vvip-68/GyverMatrixWiFi/Android/images/dot_matrix.png

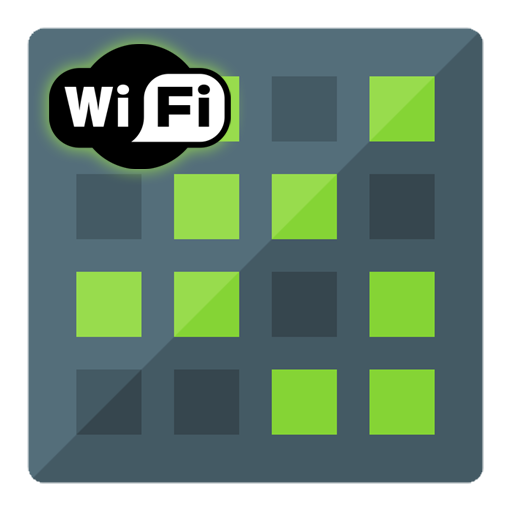
Android/images/dot_matrix.png
