vvip-68/GyverMatrixWiFi/Android/images/Hue_alpha.png

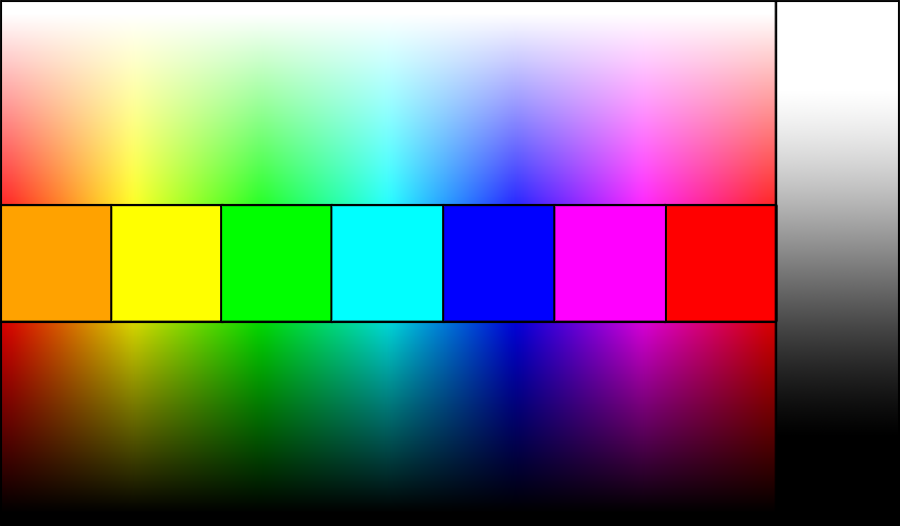
Android/images/Hue_alpha.png
