vvip-68/GyverMatrixWiFi/image decoding/gifs/8-bit_dance_red.gif

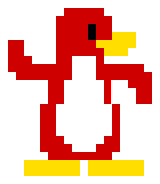
image decoding/gifs/8-bit_dance_red.gif
