vvip-68/GyverMatrixWiFi/image decoding/gifs/8bit_e78edc_811577.gif

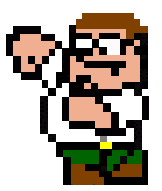
image decoding/gifs/8bit_e78edc_811577.gif
