vvip-68/GyverMatrixWiFi/image decoding/gifs/8x8/Superheroes/Superheroes.png

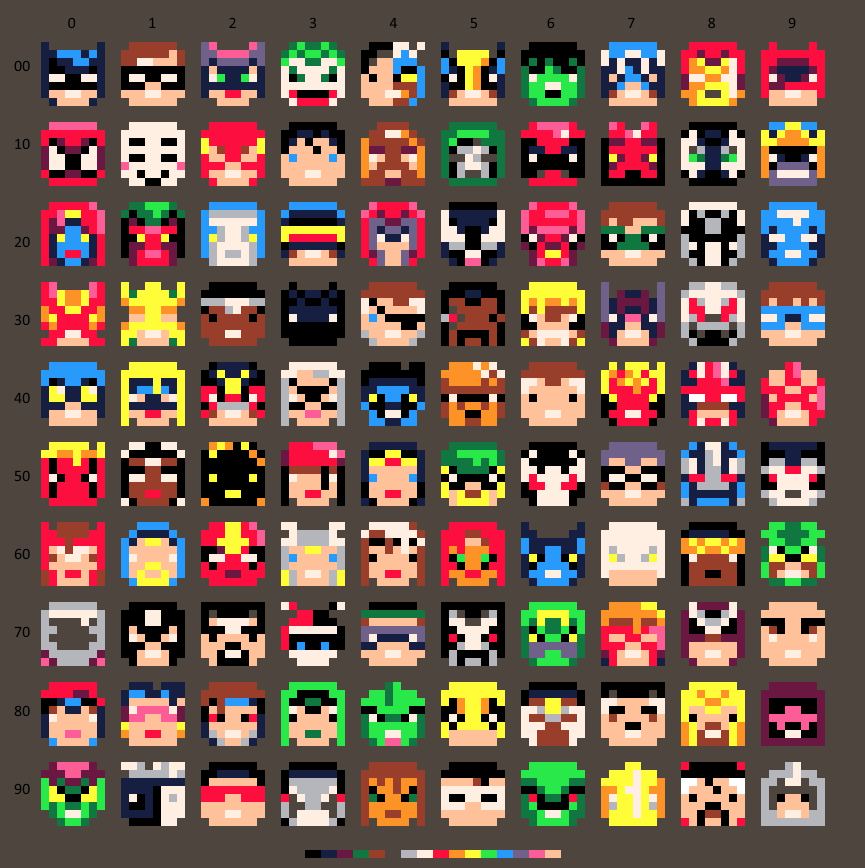
image decoding/gifs/8x8/Superheroes/Superheroes.png
