vvip-68/GyverMatrixWiFi/image decoding/gifs/8x8/VideogameCharacters/VideogameCharacters.png

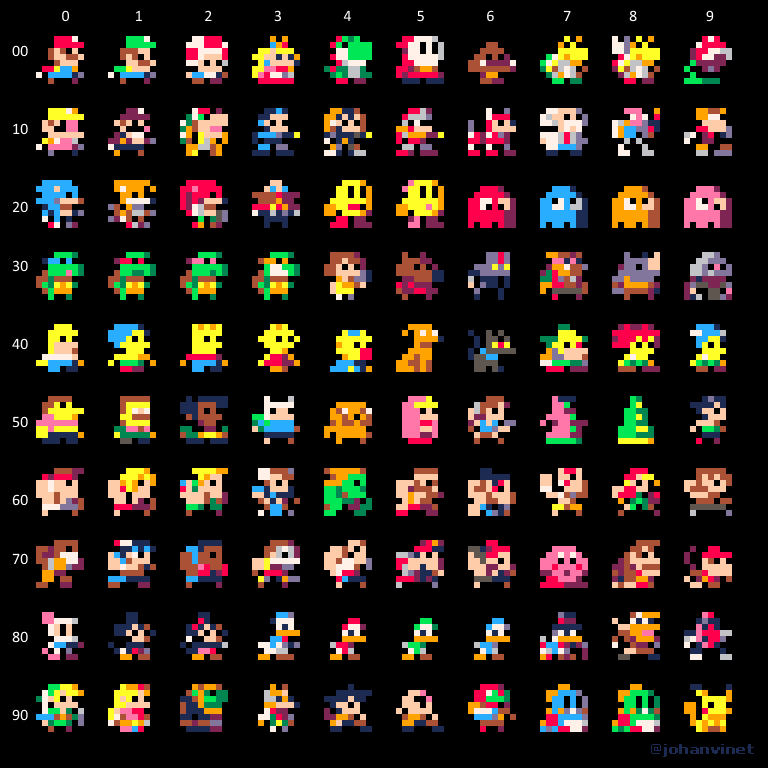
image decoding/gifs/8x8/VideogameCharacters/VideogameCharacters.png
