vvip-68/GyverMatrixWiFi/image decoding/gifs/60066832178daa8c864df8cbb47f908b34b75229.gif

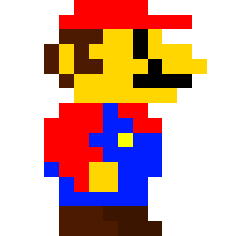
image decoding/gifs/60066832178daa8c864df8cbb47f908b34b75229.gif
