vvip-68/GyverMatrixWiFi/image decoding/gifs/asd.jpg

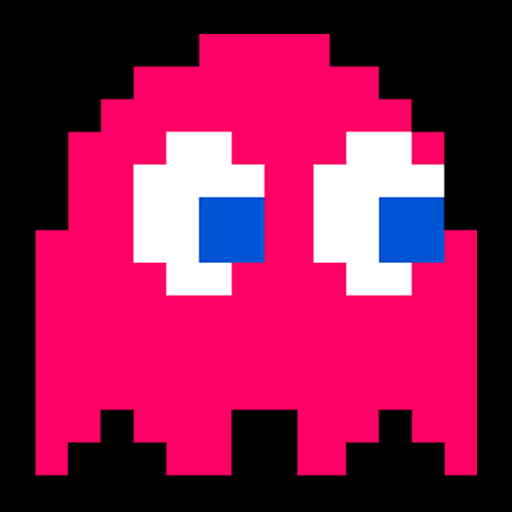
image decoding/gifs/asd.jpg
