vvip-68/GyverMatrixWiFi/image decoding/gifs/bac494cc944dbecb-me-8bit-terraria-style-gif-by-avthecreeper-on-deviantart.gif

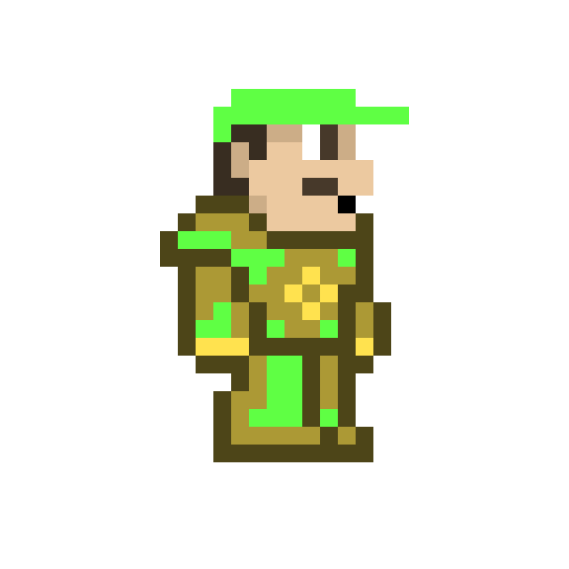
image decoding/gifs/bac494cc944dbecb-me-8bit-terraria-style-gif-by-avthecreeper-on-deviantart.gif
