vvip-68/GyverMatrixWiFi/image decoding/gifs/d8q91xd-37d3a5f7-6120-4784-a24a-eec837a43671.gif

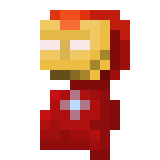
image decoding/gifs/d8q91xd-37d3a5f7-6120-4784-a24a-eec837a43671.gif
