vvip-68/GyverMatrixWiFi/image decoding/gifs/db7e7il-261c622e-b4ed-433d-9d11-8a8a13b2ce55.gif

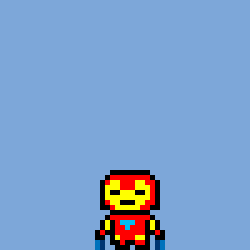
image decoding/gifs/db7e7il-261c622e-b4ed-433d-9d11-8a8a13b2ce55.gif
