vvip-68/GyverMatrixWiFi/image decoding/gifs/fire.gif

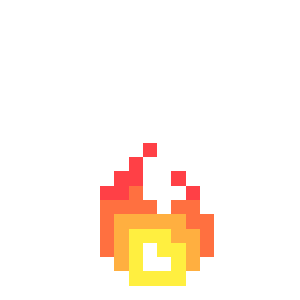
image decoding/gifs/fire.gif
