vvip-68/GyverMatrixWiFi/image decoding/gifs/fry-sprite-5fps.gif

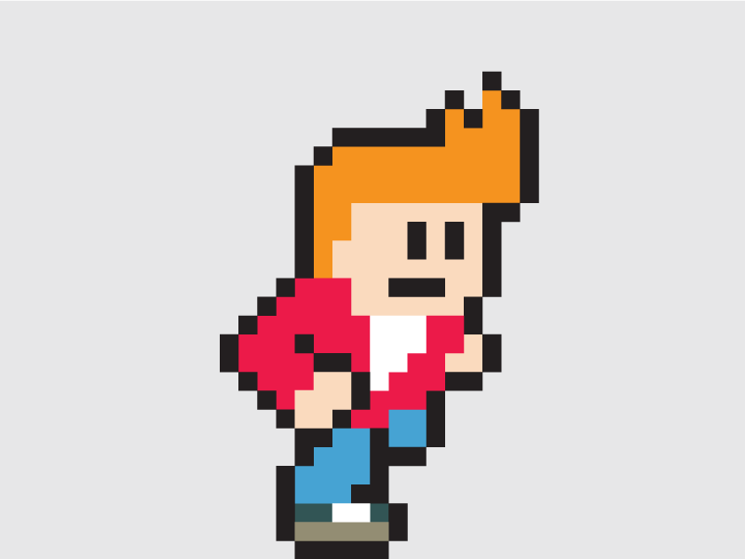
image decoding/gifs/fry-sprite-5fps.gif
