vvip-68/GyverMatrixWiFi/image decoding/gifs/megaman-running-gif-8.gif

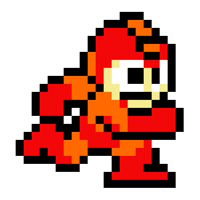
image decoding/gifs/megaman-running-gif-8.gif
