vvip-68/GyverMatrixWiFi/image decoding/gifs/source.gif

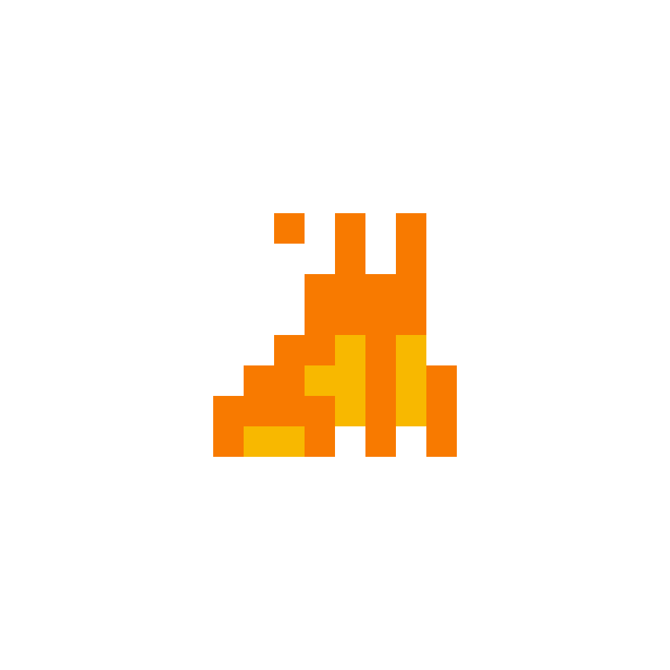
image decoding/gifs/source.gif
