vvip-68/GyverMatrixWiFi/image decoding/gifs/tenor (1).gif

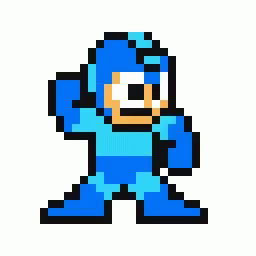
image decoding/gifs/tenor (1).gif
