vvip-68/GyverMatrixWiFi/image decoding/gifs/tenor (2).gif

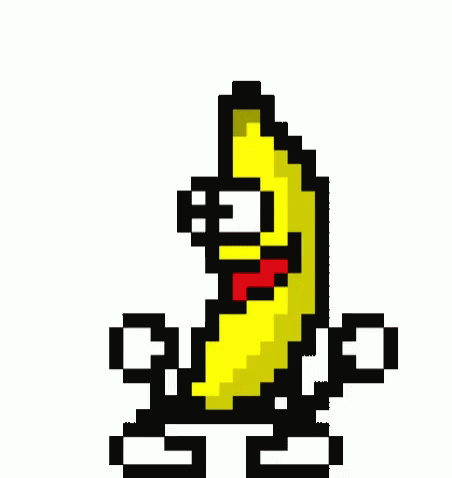
image decoding/gifs/tenor (2).gif
