vvip-68/GyverMatrixWiFi/image decoding/gifs/tenor.gif

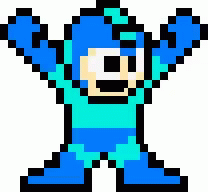
image decoding/gifs/tenor.gif
