vvip-68/GyverMatrixWiFi/image decoding/gifs/transparent-flames-8-bit-6.gif

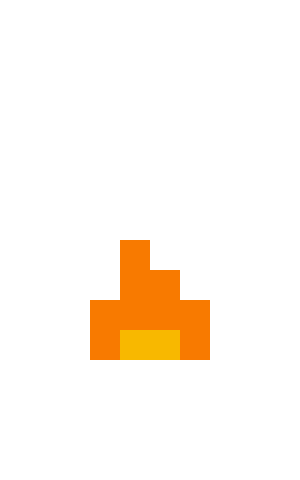
image decoding/gifs/transparent-flames-8-bit-6.gif
