vvip-68/GyverMatrixWiFi/image decoding/gifs/джэ.jpg

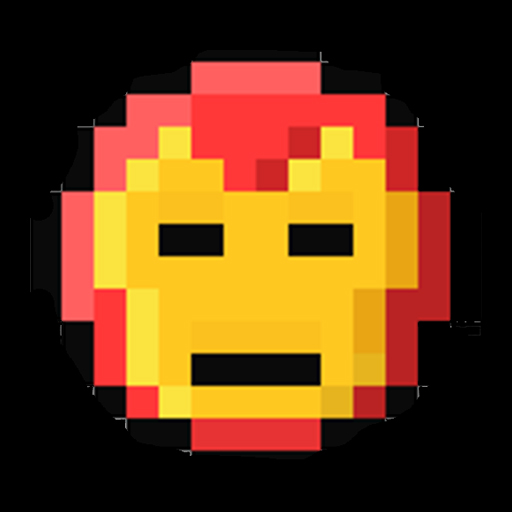
image decoding/gifs/джэ.jpg
