vvip-68/GyverMatrixWiFi/schemes/grid.png

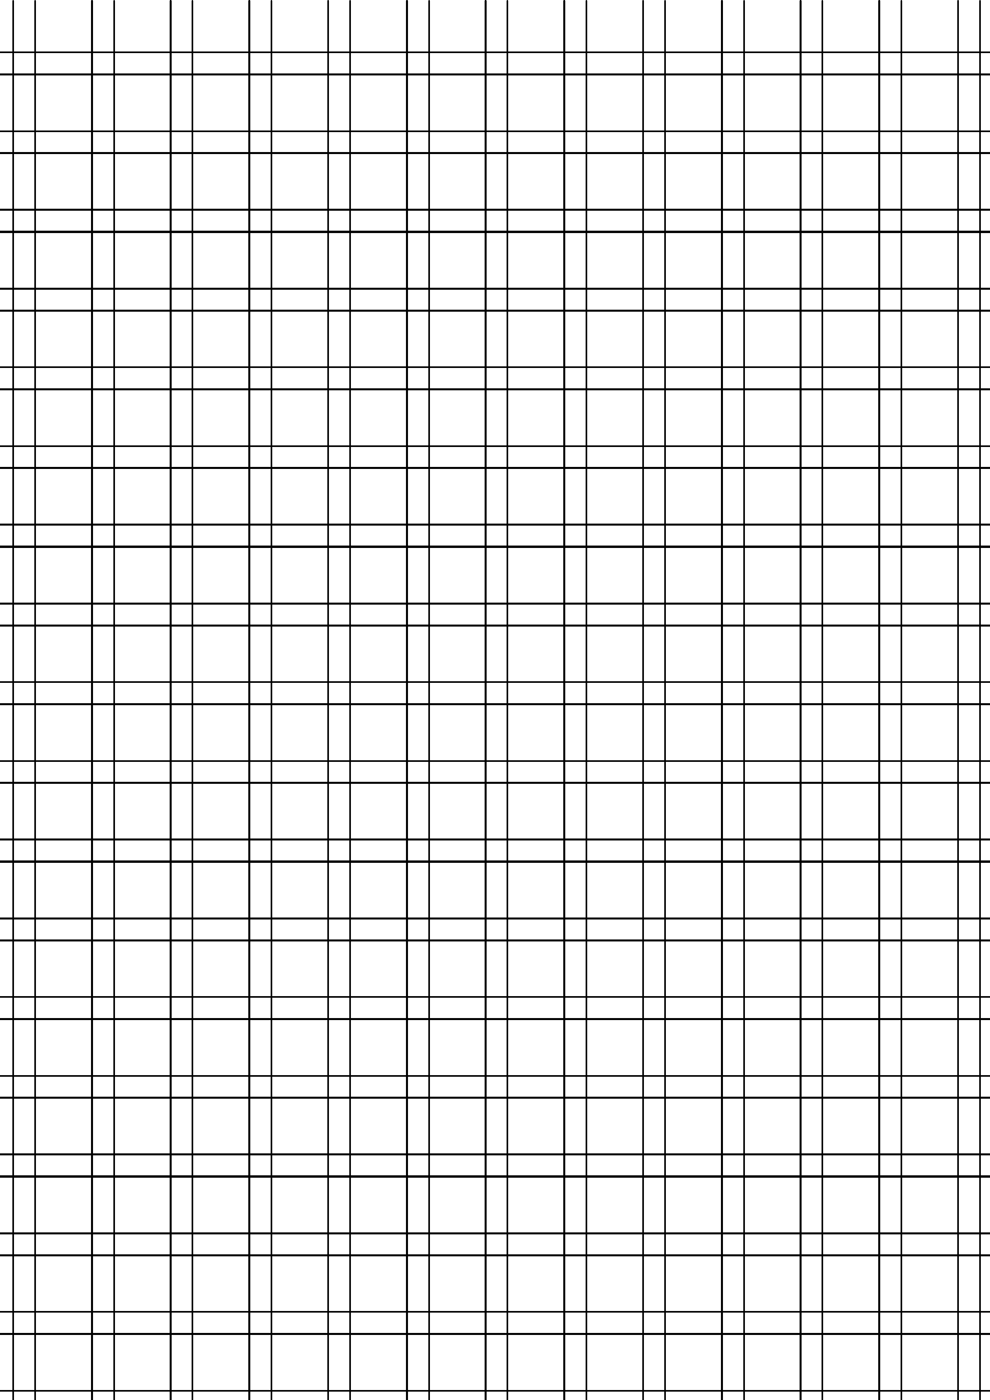
schemes/grid.png
