vvip-68/GyverMatrixWiFi/schemes/scheme4.jpg

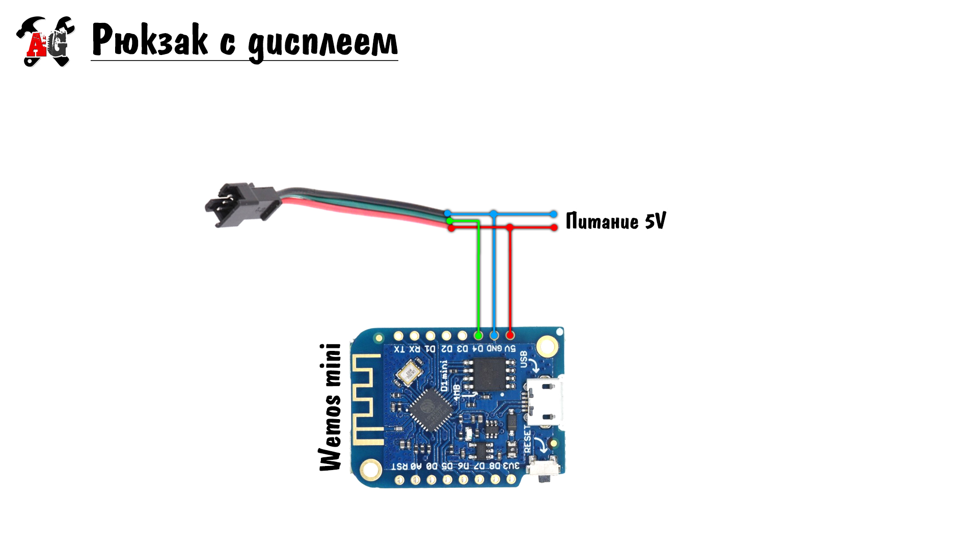
schemes/scheme4.jpg
