vvip-68/GyverMatrixWiFi/schemes/scheme5.jpg

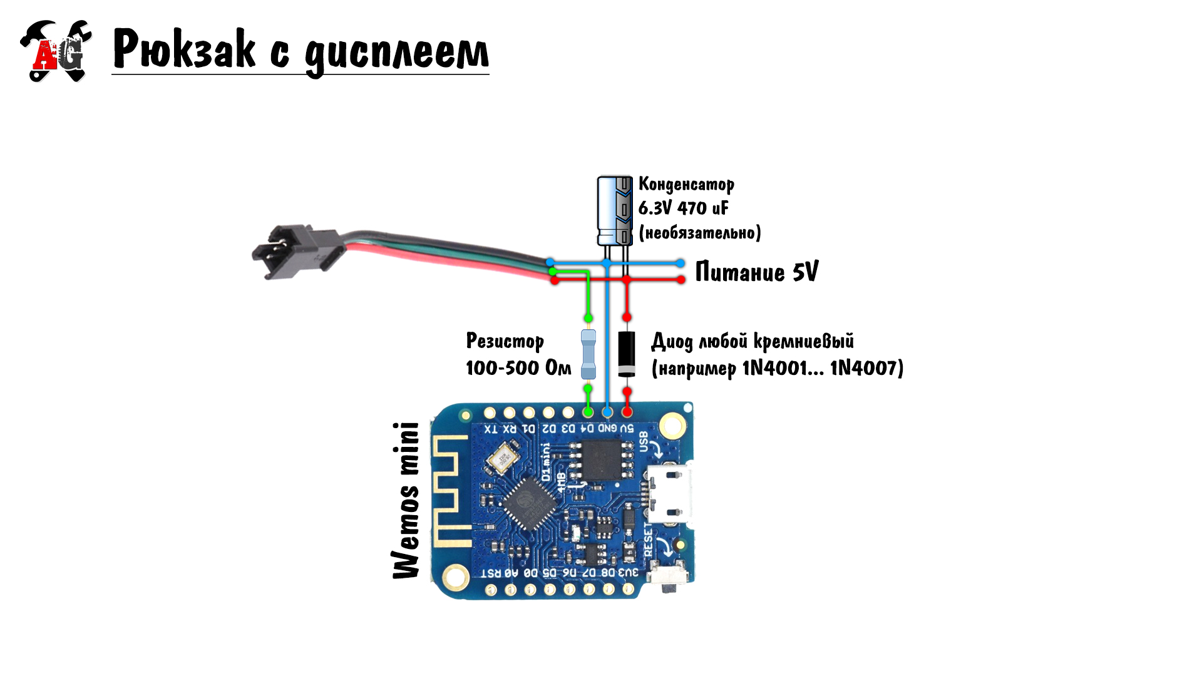
schemes/scheme5.jpg
