vvip-68/GyverMatrixWiFi/firmware/GyverMatrixOS_v1.15/custom.ino

// свой список режимов

// ************************ НАСТРОЙКИ ************************
#define SHOW_FULL_TEXT 1    // не переключать режим, пока текст не покажется весь
#define SHOW_TEXT_ONCE 1    // показывать бегущий текст только 1 раз

/*
   Режимы:
    clockRoutine();       // часы на чёрном фоне

   Эффекты:
    sparklesRoutine();    // случайные цветные гаснущие вспышки
    snowRoutine();        // снег
    matrixRoutine();      // "матрица"
    starfallRoutine();    // звездопад (кометы)
    ballRoutine();        // квадратик
    ballsRoutine();       // шарики
    rainbowRoutine();     // радуга во всю матрицу горизонтальная
    rainbowDiagonalRoutine();   // радуга во всю матрицу диагональная
    fireRoutine();        // огонь
    lightBallsRoutine()   // пейнтбол
    lightersRoutine()     // светляки

  Крутые эффекты "шума":
    madnessNoise();       // цветной шум во всю матрицу
    cloudNoise();         // облака
    lavaNoise();          // лава
    plasmaNoise();        // плазма
    rainbowNoise();       // радужные переливы
    rainbowStripeNoise(); // полосатые радужные переливы
    zebraNoise();         // зебра
    forestNoise();        // шумящий лес
    oceanNoise();         // морская вода

  Игры:
    snakeRoutine();     // змейка
    tetrisRoutine();    // тетрис
    mazeRoutine();      // лабиринт
    runnerRoutine();    // бегалка прыгалка
    arkanoidRoutine();  // арканоид

  Бегущая строка:
    fillString("Ваш текст", цвет);    // цвет вида 0x00ff25 или CRGB::Red и проч. цвета
    fillString("Ваш текст", 1);       // радужный перелив текста
    fillString("Ваш текст", 2);       // каждая буква случайным цветом!

  Рисунки и анимации:
    loadImage(<название массива>);    // основная функция вывода картинки
    imageRoutine();                   // пример использования
    animation(<n>);                   // пример анимации
*/

byte lastOverlayMode;
void customRoutine() {

  if (!gamemodeFlag || isAlarming) {

    // Беугщая строка - таймер внутри fillString (runningText.ino)
    if (!isAlarming && (thisMode == DEMO_TEXT_0 || thisMode == DEMO_TEXT_1 || thisMode == DEMO_TEXT_2)) {
      customModes(thisMode);
    } 

    // Эффекты - возможно наложение часов
    else {
      doEffectWithOverlay(thisMode); 
    }
  } 

  // Игры - таймер внутри игр
  else {
    if (!gamePaused || loadingFlag) customModes(thisMode);
  }
}

void doEffectWithOverlay(byte aMode) {

  if (effectTimer.isReady()) {

#if (OVERLAY_CLOCK == 1)
    bool loadFlag2;
    bool needOverlay = modeCode != MC_TEXT && overlayAllowed();

    if (needOverlay && lastOverlayMode == thisMode) {
      if (!loadingFlag && needUnwrap()) {
        if (showDateInClock && showDateState) {
            calendarOverlayUnwrap(CALENDAR_X, CALENDAR_Y);
        } else {
          if (CLOCK_ORIENT == 0)
            clockOverlayUnwrapH(CLOCK_X, CLOCK_Y);
          else
            clockOverlayUnwrapV(CLOCK_X, CLOCK_Y);
        }
      }
      if (loadingFlag) loadFlag2 = true;
    }
#endif

    customModes(aMode);                // режимы крутятся, пиксели мутятся

    if (millis() - showDateStateLastChange > (showDateState ? showDateDuration : showDateInterval) * 1000L) {
      showDateStateLastChange = millis();
      showDateState = !showDateState;
    }
        
#if (OVERLAY_CLOCK == 1)
    if (needOverlay) {
      if (showDateInClock && showDateState) {
        calendarOverlayWrap(CALENDAR_X, CALENDAR_Y);
      } else {
        if (CLOCK_ORIENT == 0)
          clockOverlayWrapH(CLOCK_X, CLOCK_Y);
        else  
          clockOverlayWrapV(CLOCK_X, CLOCK_Y);
      }
      lastOverlayMode = thisMode;
      if (loadFlag2) {
        setOverlayColors();
        loadFlag2 = false;
      }          
    }
    loadingFlag = false;
#endif
    FastLED.show();
  }
}

void customModes(byte aMode) {  

  switch (aMode) {    
    case DEMO_TEXT_0:              fillString(TEXT_1, CRGB::RoyalBlue); break;
    case DEMO_TEXT_1:              fillString(TEXT_2, 1); break;
    case DEMO_TEXT_2:              fillString(TEXT_3, 2); break;
    case DEMO_NOISE_MADNESS:       madnessNoise(); break;
    case DEMO_NOISE_CLOUD:         cloudNoise(); break;
    case DEMO_NOISE_LAVA:          lavaNoise(); break;
    case DEMO_NOISE_PLASMA:        plasmaNoise(); break;
    case DEMO_NOISE_RAINBOW:       rainbowNoise(); break;
    case DEMO_NOISE_RAINBOW_STRIP: rainbowStripeNoise(); break;
    case DEMO_NOISE_ZEBRA:         zebraNoise(); break;
    case DEMO_NOISE_FOREST:        forestNoise(); break;
    case DEMO_NOISE_OCEAN:         oceanNoise(); break;
    case DEMO_SNOW:                snowRoutine(); break;
    case DEMO_SPARKLES:            sparklesRoutine(); break;
    case DEMO_MATRIX:              matrixRoutine(); break;
    case DEMO_STARFALL:            starfallRoutine(); break;
    case DEMO_BALL:                ballRoutine(); break;
    case DEMO_BALLS:               ballsRoutine(); break;
    case DEMO_RAINBOW:             rainbowRoutine(); break;
    case DEMO_RAINBOW_DIAG:        rainbowDiagonalRoutine(); break;
    case DEMO_FIRE:                fireRoutine(); break;
    case DEMO_SNAKE:               snakeRoutine(); break;
    case DEMO_TETRIS:              tetrisRoutine(); break;
    case DEMO_MAZE:                mazeRoutine(); break;
    case DEMO_RUNNER:              runnerRoutine(); break;
    case DEMO_ARKANOID:            arkanoidRoutine(); break;
    case DEMO_CLOCK:               clockRoutine(); break;
    case DEMO_DAWN_ALARM:          dawnProcedure(); break;
    case DEMO_FILL_COLOR:          fillColorProcedure(); break;
    case DEMO_LIGHTERS:            lightersRoutine(); break;
    case DEMO_PAINTBALL:           lightBallsRoutine(); break;
    case DEMO_SWIRL:               swirlRoutine(); break;

    case DEMO_ANIMATION_1:         animation(1); break;
    /*
    case DEMO_ANIMATION_2:         animation(2); break;
    case DEMO_ANIMATION_3:         animation(3); break;
    case DEMO_ANIMATION_4:         animation(4); break;
    case DEMO_ANIMATION_5:         animation(5); break;
    */
    
    // Специальные режимы - доступные только для вызова из эффекта рассвета - dawnProcedure()
    case DEMO_DAWN_ALARM_SPIRAL:   dawnLampSpiral(); break;
    case DEMO_DAWN_ALARM_SQUARE:   dawnLampSquare(); break;
  }
}

// ********************* ОСНОВНОЙ ЦИКЛ РЕЖИМОВ *******************

static void nextMode() {  
#if (SMOOTH_CHANGE == 1)
  fadeMode = 0;
  modeDir = true;
#else
  nextModeHandler();
#endif
}

static void prevMode() {
#if (SMOOTH_CHANGE == 1)
  fadeMode = 0;
  modeDir = false;
#else
  prevModeHandler();
#endif
}

void nextModeHandler() {

  if (useRandomSequence) {
    setRandomMode2();
    return;
  }
  
  byte aCnt = 0;
  byte curMode = thisMode;

  loadingFlag = true;
  autoplayTimer = millis();  
  
  while (aCnt < MODES_AMOUNT) {
    // Берем следующий режим по циклу режимов
    aCnt++; thisMode++;  
    if (thisMode >= MODES_AMOUNT) thisMode = 0;

    // Если новый режим отмечен флагом "использовать" - используем его, иначе берем следующий (и проверяем его)
    if (getUsageForMode(thisMode)) break;
    
    // Если перебрали все и ни у одного нет флага "использовать" - не обращаем внимание на флаг, используем следующий
    if (aCnt >= MODES_AMOUNT) {
      thisMode = curMode++;
      if (thisMode >= MODES_AMOUNT) thisMode = 0;
      break;
    }  
    #if defined(ESP8266)
    ESP.wdtFeed();  
    #endif
  }

  setModeByModeId(thisMode); 
  autoplayTimer = millis();

  FastLED.clear();
  FastLED.show();
  FastLED.setBrightness(globalBrightness);
}

void prevModeHandler() {

  if (useRandomSequence) {
    setRandomMode2();
    return;
  }

  byte aCnt = 0;
  byte curMode = thisMode;

  while (aCnt < MODES_AMOUNT) {
    // Берем предыдущий режим по циклу режимов
    aCnt++; thisMode--; // thisMode: byte => при переполнении вернет 255 
    if (thisMode >= MODES_AMOUNT) thisMode = MODES_AMOUNT - 1;

    // Если новый режим отмечен флагом "использовать" - используем его, иначе берем следующий (и проверяем его)
    if (getUsageForMode(thisMode)) break;
    
    // Если перебрали все и ни у адного нет флага "использовать" - не обращаем внимание на флаг, используем следующий
    if (aCnt >= MODES_AMOUNT) {
      thisMode = curMode--; // thisMode: byte => при переполнении вернет 255
      if (thisMode >= MODES_AMOUNT) thisMode = MODES_AMOUNT - 1;
      break;
    }   
    
    #if defined(ESP8266)    
    ESP.wdtFeed(); 
    #endif
  }
  
  setModeByModeId(thisMode); 
  autoplayTimer = millis();
  
  FastLED.clear();
  FastLED.show();
  FastLED.setBrightness(globalBrightness);
}

void setTimersForMode(byte aMode) {
  if (runningFlag || aMode == DEMO_TEXT_0 || aMode == DEMO_TEXT_1 || aMode == DEMO_TEXT_2) {
    // Это бегущий текст  
    scrollSpeed = getScrollSpeed();
    if (scrollSpeed == 0) scrollSpeed = 1;
    scrollTimer.setInterval(scrollSpeed);
  } 
  else if (aMode == DEMO_PAINTBALL) {
    // Это эффект Пейнтбол
    effectSpeed = getEffectSpeed(EFFECT_PAINTBALL);  // В этом эффекте параметр "скорость" влияет на количество шариков 1..4 
    effectTimer.setInterval(10);                     // Эффект работает только на высокой скорости
  } 
  /*
  else if (aMode == DEMO_SWIRL) {
    // Это эффект Swirl
    effectSpeed = getEffectSpeed(EFFECT_SWIRL);      // 
    effectTimer.setInterval(10);                     // Этот эффект работает только на высокой скорости
  } 
  */
  else {
    byte tmp_effect = mapModeToEffect(aMode);
    if (tmp_effect != 255) {
      effectSpeed = getEffectSpeed(tmp_effect);
      if (effectSpeed == 0) effectSpeed = 1;
      effectTimer.setInterval(effectSpeed);
      gifTimer.setInterval(effectSpeed);
    } else {
      byte tmp_game = mapModeToGame(aMode);
      if (tmp_game != 255) {
        gameSpeed = getGameSpeed(game);
        if (gameSpeed == 0) gameSpeed = 1;
        gameTimer.setInterval(gameSpeed);
      }
    }
  }
}

boolean getUsageForMode(byte aMode) {
  if (aMode == DEMO_TEXT_0 || aMode == DEMO_TEXT_1 || aMode == DEMO_TEXT_2) {
    // Это бегущий текст  
    return getUseTextInDemo();
  } else {
    
    byte tmp_effect = mapModeToEffect(aMode);
    if (tmp_effect != 255) {
      return getEffectUsage(tmp_effect);
    }

    byte tmp_game = mapModeToGame(aMode);
    if (tmp_game != 255) {
      return getGameUsage(tmp_game);
    }

    return true;
  }
}

int fadeBrightness;
int fadeStepCount = 10;     // За сколько шагов убирать/добавлять яркость при смене режимов
int fadeStepValue = 5;      // Шаг убавления яркости

#if (SMOOTH_CHANGE == 1)
void modeFader() {
  if (fadeMode == 0) {
    fadeMode = 1;
    fadeStepValue = fadeBrightness / fadeStepCount;
    if (fadeStepValue < 1) fadeStepValue = 1;
  } else if (fadeMode == 1) {
    if (changeTimer.isReady()) {
      fadeBrightness -= fadeStepValue;
      if (fadeBrightness < 0) {
        fadeBrightness = 0;
        fadeMode = 2;
      }
      FastLED.setBrightness(fadeBrightness);
    }
  } else if (fadeMode == 2) {
    fadeMode = 3;
    if (modeDir) nextModeHandler();
    else prevModeHandler();
  } else if (fadeMode == 3) {
    if (changeTimer.isReady()) {
      fadeBrightness += fadeStepValue;
      if (fadeBrightness > globalBrightness) {
        fadeBrightness = globalBrightness;
        fadeMode = 4;
      }
      FastLED.setBrightness(fadeBrightness);
    }
  }
}
#endif

void checkIdleState() {
  
#if (SMOOTH_CHANGE == 1)
  modeFader();
#endif

  if (idleState) {
    if (fullTextFlag && SHOW_TEXT_ONCE) {
      fullTextFlag = false;
      autoplayTimer = millis();
      if (AUTOPLAY) nextMode();
    }
    
    if ((millis() - autoplayTimer > autoplayTime) && AUTOPLAY) {    // таймер смены режима
      autoplayTimer = millis();
      if (modeCode == MC_TEXT && SHOW_FULL_TEXT) {    // режим текста
        if (fullTextFlag) {
          fullTextFlag = false;
          nextMode();
        }
      } else {
        nextMode();
      }
    }
  } else {
    if (idleTimer.isReady()) {                  // таймер холостого режима. 
      idleState = true;
      autoplayTimer = millis();
      gameDemo = true;

      BTcontrol = false;
      loadingFlag = true;
      runningFlag = false;
      controlFlag = false;                      // После начала игры пока не трогаем кнопки - игра автоматическая 
      drawingFlag = false;
      gamemodeFlag = false;
      gamePaused = false;

      AUTOPLAY = true;
      
      FastLED.clear();
      FastLED.show();      
    }
  }  
}

byte mapEffectToMode(byte effect) {
  byte tmp_mode = 255;
  
  switch (effect) {
    case EFFECT_SNOW:                tmp_mode = DEMO_SNOW; break;                 // snowRoutine();
    case EFFECT_BALL:                tmp_mode = DEMO_BALL; break;                 // ballRoutine();
    case EFFECT_RAINBOW:             tmp_mode = DEMO_RAINBOW; break;              // rainbowRoutine();
    case EFFECT_FIRE:                tmp_mode = DEMO_FIRE; break;                 // fireRoutine()
    case EFFECT_MATRIX:              tmp_mode = DEMO_MATRIX; break;               // matrixRoutine();
    case EFFECT_BALLS:               tmp_mode = DEMO_BALLS; break;                // ballsRoutine();
    case EFFECT_CLOCK:               tmp_mode = DEMO_CLOCK; break;                // clockRoutine();
    case EFFECT_STARFALL:            tmp_mode = DEMO_STARFALL; break;             // starfallRoutine()
    case EFFECT_SPARKLES:            tmp_mode = DEMO_SPARKLES; break;             // sparklesRoutine()
    case EFFECT_RAINBOW_DIAG:        tmp_mode = DEMO_RAINBOW_DIAG; break;         // rainbowDiagonalRoutine();
    case EFFECT_NOISE_MADNESS:       tmp_mode = DEMO_NOISE_MADNESS;  break;       // madnessNoise();
    case EFFECT_NOISE_CLOUD:         tmp_mode = DEMO_NOISE_CLOUD;  break;         // cloudNoise();
    case EFFECT_NOISE_LAVA:          tmp_mode = DEMO_NOISE_LAVA;  break;          // lavaNoise();
    case EFFECT_NOISE_PLASMA:        tmp_mode = DEMO_NOISE_PLASMA;  break;        // plasmaNoise();
    case EFFECT_NOISE_RAINBOW:       tmp_mode = DEMO_NOISE_RAINBOW;  break;       // rainbowNoise();
    case EFFECT_NOISE_RAINBOW_STRIP: tmp_mode = DEMO_NOISE_RAINBOW_STRIP;  break; // rainbowStripeNoise();
    case EFFECT_NOISE_ZEBRA:         tmp_mode = DEMO_NOISE_ZEBRA;  break;         // zebraNoise();
    case EFFECT_NOISE_FOREST:        tmp_mode = DEMO_NOISE_FOREST; break;         // forestNoise();
    case EFFECT_NOISE_OCEAN:         tmp_mode = DEMO_NOISE_OCEAN; break;          // oceanNoise();
    case EFFECT_PAINTBALL:           tmp_mode = DEMO_PAINTBALL; break;            // lightBallsRoutine()
    case EFFECT_SWIRL:               tmp_mode = DEMO_SWIRL; break;                // swirlRoutine()
    case EFFECT_LIGHTERS:            tmp_mode = DEMO_LIGHTERS; break;             // lightersRoutine()
    case EFFECT_DAWN_ALARM:          tmp_mode = DEMO_DAWN_ALARM; break;           // dawnProcedure();
    case EFFECT_FILL_COLOR:          tmp_mode = DEMO_FILL_COLOR; break;           // fillColorProcedure();
    case EFFECT_ANIMATION_1:         tmp_mode = DEMO_ANIMATION_1; break;          // animation(1);
    /*
    case EFFECT_ANIMATION_2:         tmp_mode = DEMO_ANIMATION_2; break;          // animation(2);
    case EFFECT_ANIMATION_3:         tmp_mode = DEMO_ANIMATION_3; break;          // animation(3);
    case EFFECT_ANIMATION_4:         tmp_mode = DEMO_ANIMATION_4; break;          // animation(4);
    case EFFECT_ANIMATION_5:         tmp_mode = DEMO_ANIMATION_5; break;          // animation(5);
    */
  }

  return tmp_mode;
}

byte mapEffectToModeCode(byte effect) {
  byte tmp_mode = 255;
  
  switch (effect) {
    case EFFECT_SNOW:                tmp_mode = MC_SNOW; break;                 // snowRoutine();
    case EFFECT_BALL:                tmp_mode = MC_BALL; break;                 // ballRoutine();
    case EFFECT_RAINBOW:             tmp_mode = MC_RAINBOW; break;              // rainbowRoutine();
    case EFFECT_FIRE:                tmp_mode = MC_FIRE; break;                 // fireRoutine()
    case EFFECT_MATRIX:              tmp_mode = MC_MATRIX; break;               // matrixRoutine();
    case EFFECT_BALLS:               tmp_mode = MC_BALLS; break;                // ballsRoutine();
    case EFFECT_CLOCK:               tmp_mode = MC_CLOCK; break;                // clockRoutine();
    case EFFECT_STARFALL:            tmp_mode = MC_STARFALL; break;             // starfallRoutine()
    case EFFECT_SPARKLES:            tmp_mode = MC_SPARKLES; break;             // sparklesRoutine()
    case EFFECT_RAINBOW_DIAG:        tmp_mode = MC_RAINBOW_DIAG; break;         // rainbowDiagonalRoutine();
    case EFFECT_NOISE_MADNESS:       tmp_mode = MC_NOISE_MADNESS;  break;       // madnessNoise();
    case EFFECT_NOISE_CLOUD:         tmp_mode = MC_NOISE_CLOUD;  break;         // cloudNoise();
    case EFFECT_NOISE_LAVA:          tmp_mode = MC_NOISE_LAVA;  break;          // lavaNoise();
    case EFFECT_NOISE_PLASMA:        tmp_mode = MC_NOISE_PLASMA;  break;        // plasmaNoise();
    case EFFECT_NOISE_RAINBOW:       tmp_mode = MC_NOISE_RAINBOW;  break;       // rainbowNoise();
    case EFFECT_NOISE_RAINBOW_STRIP: tmp_mode = MC_NOISE_RAINBOW_STRIP;  break; // rainbowStripeNoise();
    case EFFECT_NOISE_ZEBRA:         tmp_mode = MC_NOISE_ZEBRA;  break;         // zebraNoise();
    case EFFECT_NOISE_FOREST:        tmp_mode = MC_NOISE_FOREST; break;         // forestNoise();
    case EFFECT_NOISE_OCEAN:         tmp_mode = MC_NOISE_OCEAN; break;          // oceanNoise();
    case EFFECT_PAINTBALL:           tmp_mode = MC_PAINTBALL; break;            // lightBallsRoutine()
    case EFFECT_SWIRL:               tmp_mode = MC_SWIRL; break;                // swirlRoutine()
    case EFFECT_LIGHTERS:            tmp_mode = MC_LIGHTERS; break;             // lightersRoutine()
    case EFFECT_ANIMATION_1:         tmp_mode = MC_IMAGE; break;                // animation(1);
    /*
    case EFFECT_ANIMATION_2:         tmp_mode = MC_IMAGE; break;                // animation(2);
    case EFFECT_ANIMATION_3:         tmp_mode = MC_IMAGE; break;                // animation(3);
    case EFFECT_ANIMATION_4:         tmp_mode = MC_IMAGE; break;                // animation(4);
    case EFFECT_ANIMATION_5:         tmp_mode = MC_IMAGE; break;                // animation(5);
    */
    case EFFECT_DAWN_ALARM:          tmp_mode = MC_DAWN_ALARM; break;           // dawnProcedure();
    case EFFECT_FILL_COLOR:          tmp_mode = MC_FILL_COLOR; break;           // fillColorProcedure();
  }

  return tmp_mode;
}

byte mapGameToMode(byte game) {
  byte tmp_mode = 255;
  
  switch (game) {
    case GAME_SNAKE:    tmp_mode = DEMO_SNAKE;    break;  // snakeRoutine(); 
    case GAME_TETRIS:   tmp_mode = DEMO_TETRIS;   break;  // tetrisRoutine();
    case GAME_MAZE:     tmp_mode = DEMO_MAZE;     break;  // mazeRoutine();
    case GAME_RUNNER:   tmp_mode = DEMO_RUNNER;   break;  // runnerRoutine();
    case GAME_ARKANOID: tmp_mode = DEMO_ARKANOID; break;  // arkanoidRoutine();
  }

  return tmp_mode;
}

byte mapModeToEffect(byte aMode) {
  byte tmp_effect = 255;
  // Если режима нет в списке - ему нет соответствия среди эффектов - значит это игра или бегущий текст
  switch (aMode) {
    case DEMO_NOISE_MADNESS:        tmp_effect = EFFECT_NOISE_MADNESS; break;       // madnessNoise();
    case DEMO_NOISE_CLOUD:          tmp_effect = EFFECT_NOISE_CLOUD; break;         // cloudNoise();
    case DEMO_NOISE_LAVA:           tmp_effect = EFFECT_NOISE_LAVA; break;          // lavaNoise();
    case DEMO_NOISE_PLASMA:         tmp_effect = EFFECT_NOISE_PLASMA; break;        // plasmaNoise();
    case DEMO_NOISE_RAINBOW:        tmp_effect = EFFECT_NOISE_RAINBOW; break;       // rainbowNoise();
    case DEMO_NOISE_RAINBOW_STRIP:  tmp_effect = EFFECT_NOISE_RAINBOW_STRIP; break; // rainbowStripeNoise();
    case DEMO_NOISE_ZEBRA:          tmp_effect = EFFECT_NOISE_ZEBRA; break;         // zebraNoise();
    case DEMO_NOISE_FOREST:         tmp_effect = EFFECT_NOISE_FOREST; break;        // forestNoise();
    case DEMO_NOISE_OCEAN:          tmp_effect = EFFECT_NOISE_OCEAN; break;         // oceanNoise();
    case DEMO_SNOW:                 tmp_effect = EFFECT_SNOW;  break;               // snowRoutine();
    case DEMO_SPARKLES:             tmp_effect = EFFECT_SPARKLES; break;            // sparklesRoutine()
    case DEMO_MATRIX:               tmp_effect = EFFECT_MATRIX;  break;             // matrixRoutine();
    case DEMO_STARFALL:             tmp_effect = EFFECT_STARFALL; break;            // starfallRoutine()
    case DEMO_BALL:                 tmp_effect = EFFECT_BALL;  break;               // ballRoutine();
    case DEMO_BALLS:                tmp_effect = EFFECT_BALLS;  break;              // ballsRoutine();
    case DEMO_RAINBOW:              tmp_effect = EFFECT_RAINBOW;  break;            // rainbowRoutine();
    case DEMO_RAINBOW_DIAG:         tmp_effect = EFFECT_RAINBOW_DIAG; break;        // rainbowDiagonalRoutine();
    case DEMO_FIRE:                 tmp_effect = EFFECT_FIRE;  break;               // fireRoutine()
    case DEMO_CLOCK:                tmp_effect = EFFECT_CLOCK;  break;              // clockRoutine()
    case DEMO_DAWN_ALARM:           tmp_effect = EFFECT_DAWN_ALARM; break;          // alarmProcedure();
    case DEMO_FILL_COLOR:           tmp_effect = EFFECT_FILL_COLOR; break;          // fillColorProcedure();
    case DEMO_PAINTBALL:            tmp_effect = EFFECT_PAINTBALL;  break;          // lightBallsRoutine()
    case DEMO_SWIRL:                tmp_effect = EFFECT_SWIRL; break;               // swirlRoutine()
    case DEMO_LIGHTERS:             tmp_effect = EFFECT_LIGHTERS;  break;           // lightersRoutine()
    
    case DEMO_ANIMATION_1:          tmp_effect = EFFECT_ANIMATION_1; break;         // animation(1);
    /*
    case DEMO_ANIMATION_2:          tmp_effect = EFFECT_ANIMATION_2; break;         // animation(2);
    case DEMO_ANIMATION_3:          tmp_effect = EFFECT_ANIMATION_3; break;         // animation(3);
    case DEMO_ANIMATION_4:          tmp_effect = EFFECT_ANIMATION_4; break;         // animation(4);
    case DEMO_ANIMATION_5:          tmp_effect = EFFECT_ANIMATION_5; break;         // animation(5);
    */

    case DEMO_TEXT_0 :  break;      // Бегущий текст
    case DEMO_TEXT_1 :  break;      // Бегущий текст
    case DEMO_TEXT_2 :  break;      // Бегущий текст

    case DEMO_SNAKE: break;         // snakeRoutine(); 
    case DEMO_TETRIS: break;        // tetrisRoutine();
    case DEMO_MAZE: break;          // mazeRoutine();
    case DEMO_RUNNER: break;        // runnerRoutine();
    case DEMO_ARKANOID: break;      // arkanoidRoutine();    
  }
  return tmp_effect;
}

byte mapModeToGame(byte aMode) {
  byte tmp_game = 255;
  // Если режима нет в списке - ему нет соответствия среди тгр - значит это эффект или бегущий текст
  switch (aMode) {
    case DEMO_NOISE_MADNESS:        break;       // madnessNoise();
    case DEMO_NOISE_CLOUD:          break;       // cloudNoise();
    case DEMO_NOISE_LAVA:           break;       // lavaNoise();
    case DEMO_NOISE_PLASMA:         break;       // plasmaNoise();
    case DEMO_NOISE_RAINBOW:        break;       // rainbowNoise();
    case DEMO_NOISE_RAINBOW_STRIP:  break;       // rainbowStripeNoise();
    case DEMO_NOISE_ZEBRA:          break;       // zebraNoise();
    case DEMO_NOISE_FOREST:         break;       // forestNoise();
    case DEMO_NOISE_OCEAN:          break;       // oceanNoise();
    case DEMO_SNOW:                 break;       // snowRoutine();
    case DEMO_SPARKLES:             break;       // sparklesRoutine()
    case DEMO_MATRIX:               break;       // matrixRoutine();
    case DEMO_STARFALL:             break;       // starfallRoutine()
    case DEMO_BALL:                 break;       // ballRoutine();
    case DEMO_BALLS:                break;       // ballsRoutine();
    case DEMO_RAINBOW:              break;       // rainbowRoutine();
    case DEMO_RAINBOW_DIAG:         break;       // rainbowDiagonalRoutine();
    case DEMO_FIRE:                 break;       // fireRoutine()
    case DEMO_DAWN_ALARM:           break;       // dawnProcedure(); 
    case DEMO_FILL_COLOR:           break;       // fillColorProcedure(); 
    case DEMO_PAINTBALL:            break;       // lightBallsRoutine()
    case DEMO_SWIRL:                break;       // swirlRoutine()
    case DEMO_LIGHTERS:             break;       // lightersRoutine()
    case DEMO_ANIMATION_1:          break;       // animation(1);
    /*
    case DEMO_ANIMATION_2:          break;       // animation(2);
    case DEMO_ANIMATION_3:          break;       // animation(3);
    case DEMO_ANIMATION_4:          break;       // animation(4);
    case DEMO_ANIMATION_5:          break;       // animation(5);
    */
    case DEMO_TEXT_0:               break;       // Бегущий текст
    case DEMO_TEXT_1:               break;       // Бегущий текст
    case DEMO_TEXT_2:               break;       // Бегущий текст

    case DEMO_SNAKE:    tmp_game = GAME_SNAKE;    break;     // snakeRoutine(); 
    case DEMO_TETRIS:   tmp_game = GAME_TETRIS;   break;     // tetrisRoutine();
    case DEMO_MAZE:     tmp_game = GAME_MAZE;     break;     // mazeRoutine();
    case DEMO_RUNNER:   tmp_game = GAME_RUNNER;   break;     // runnerRoutine();
    case DEMO_ARKANOID: tmp_game = GAME_ARKANOID; break;     // arkanoidRoutine();

    case DEMO_CLOCK:                break;  // clockRoutine();     
  }
  return tmp_game;
}

// Соответствие индекса в списке эффектов, доступных в качестве будильника индексам списка известных эффектов
byte mapAlarmToEffect(byte alrmIdx) {
  // ALARM_LIST  F("Снегопад,Шарик,Радуга,Огонь,The Matrix,Шарики,     Звездопад,Конфетти,Радуга диагональная,Цветной шум,Облака,Лава,Плазма,Радужные переливы,Полосатые переливы,Зебра,Шумящий лес,Морской прибой,      Рассвет,Анимация 1,Анимация 2,Анимация 3,Анимация 4,Анимация 5")
  // EFFECT_LIST F("Снегопад,Шарик,Радуга,Огонь,The Matrix,Шарики,Часы,Звездопад,Конфетти,Радуга диагональная,Цветной шум,Облака,Лава,Плазма,Радужные переливы,Полосатые переливы,Зебра,Шумящий лес,Морской прибой,Лампа,Рассвет,Анимация 1,Анимация 2,Анимация 3,Анимация 4,Анимация 5")
  // const byte ALARM_LIST_IDX[] PROGMEM = {EFFECT_SNOW, EFFECT_BALL, EFFECT_RAINBOW, EFFECT_FIRE, EFFECT_MATRIX, EFFECT_BALLS,
  //                                        EFFECT_STARFALL, EFFECT_SPARKLES, EFFECT_RAINBOW_DIAG, EFFECT_NOISE_MADNESS, EFFECT_NOISE_CLOUD,
  //                                        EFFECT_NOISE_LAVA, EFFECT_NOISE_PLASMA, EFFECT_NOISE_RAINBOW, EFFECT_NOISE_RAINBOW_STRIP, 
  //                                        EFFECT_NOISE_ZEBRA, EFFECT_NOISE_FOREST, EFFECT_NOISE_OCEAN, EFFECT_DAWN_ALARM, 
  //                                        EFFECT_ANIMATION_1, EFFECT_ANIMATION_2, EFFECT_ANIMATION_3, EFFECT_ANIMATION_4, EFFECT_ANIMATION_5};
  return pgm_read_byte(&(ALARM_LIST_IDX[alrmIdx]));
}

// Соответствие индекса в списке известных эффектов индексам списка эффектов, доступных в качестве будильника
byte mapEffectToAlarm(byte effect) {
  for(byte i=0; i<sizeof(ALARM_LIST_IDX); i++) {
    if (mapAlarmToEffect(i) == effect) return i;
  }
  return sizeof(ALARM_LIST_IDX) - 1; // последний эффект в списке = "Рассвет"
}
