vvip-68/GyverMatrixWiFi/firmware/GyverMatrixOS_v1.15/bitmap4.h

const uint16_t ironMan0[] PROGMEM = {
0x0000, 0x0000, 0x0000, 0x0000, 0x0000, 0x0000, 0x0000, 0x0000, 0x0000, 0x0000, 0x0000, 0x0000, 0x0000, 0x0000, 0x0000, 0x0000, 
0x0000, 0x0000, 0x0000, 0x0000, 0x0000, 0x0000, 0xF3EA, 0xFC8C, 0xF3EA, 0xE2C9, 0xE289, 0xE289, 0x0000, 0x0000, 0x0000, 0x0000, 
0x0000, 0x0000, 0x0000, 0x0000, 0x0000, 0xFEB4, 0xFE12, 0xFD0F, 0xFE53, 0xF653, 0xF631, 0xEC4C, 0xE289, 0x0000, 0x0000, 0x0000, 
0x0000, 0x0000, 0x0000, 0x0000, 0x0000, 0xF6F4, 0xF6D3, 0xF631, 0xF6D3, 0xFF35, 0xFF13, 0xE4AD, 0xDA28, 0xE289, 0x0000, 0x0000, 
0x0000, 0x0000, 0x0000, 0x0000, 0x0000, 0xFF3A, 0xF738, 0xF6D5, 0xFF3A, 0xFF36, 0xFEF3, 0xDC8D, 0xD1C8, 0xDA29, 0x0000, 0x0000, 
0x0000, 0x0000, 0x0000, 0x0000, 0x0000, 0xFF7B, 0xFF5A, 0xF6F6, 0xFF7B, 0xFF36, 0xEEB2, 0xD44C, 0xC968, 0xD188, 0x0000, 0x0000, 
0x0000, 0x0000, 0x0000, 0x0000, 0x0000, 0xFF15, 0xFF14, 0xF6D3, 0xFF15, 0xF6B2, 0xE650, 0xCBEB, 0xC968, 0xD188, 0x0000, 0x0000, 
0x0000, 0x0000, 0x0000, 0x0000, 0x0000, 0xF6D2, 0xEE91, 0xEEB1, 0xF6B2, 0xE630, 0xE650, 0xD42C, 0xC968, 0x0000, 0x0000, 0x0000, 
0x0000, 0x0000, 0x0000, 0x0000, 0x0000, 0x0000, 0x0000, 0x0000, 0xC249, 0xCAA9, 0xC208, 0x0000, 0x0000, 0x0000, 0x0000, 0x0000, 
0x0000, 0x0000, 0x0000, 0x0000, 0x0000, 0x0000, 0xE1C9, 0xDACE, 0xD24C, 0xD188, 0xC968, 0x0000, 0x0000, 0x0000, 0x0000, 0x0000, 
0x0000, 0x0000, 0x0000, 0x0000, 0x0000, 0x0000, 0xDAEE, 0xDD57, 0xDD17, 0xDA6C, 0xD188, 0xC9A8, 0x0000, 0x0000, 0x0000, 0x0000, 
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
ironMan10, ironMan11, ironMan12, ironMan13, ironMan14, ironMan15, ironMan16, ironMan17, ironMan18, ironMan19, 
ironMan20, ironMan21, ironMan22, ironMan23, ironMan24, ironMan25, ironMan26, ironMan27, ironMan28, ironMan29, 
ironMan30, ironMan31};
