vvip-68/GyverMatrixWiFi/firmware/GyverMatrixOS_v1.15/bitmap5.h

const uint16_t characters0[] PROGMEM = {
0x0000, 0x0000, 0x0000, 0x0000, 0x0000, 0x0000, 0xF813, 0xF813, 0xF813, 0xF813, 0xF813, 0xF813, 0xFFDE, 0xFFDE, 0x0000, 0x0000, 
0x0000, 0x0000, 0x0000, 0x0000, 0x0000, 0x0000, 0xF813, 0xF813, 0xF813, 0xF813, 0xF813, 0xF813, 0xFFDE, 0xFFDE, 0x0000, 0x0000, 
0x0000, 0x0000, 0x0000, 0x0000, 0x0000, 0x0000, 0xF813, 0xF813, 0xF813, 0xF813, 0xF813, 0xF813, 0xF813, 0xF813, 0xF813, 0xF813, 
0x0000, 0x0000, 0x0000, 0x0000, 0x0000, 0x0000, 0xF813, 0xF813, 0xF813, 0xF813, 0xF813, 0xF813, 0xF813, 0xF813, 0xF813, 0xF813, 
0x0000, 0x0000, 0x0000, 0x0000, 0xDC90, 0xDC90, 0xFF3B, 0xFF3B, 0xDC90, 0xDC90, 0x0000, 0x0000, 0xFF3B, 0xFF3B, 0x0000, 0x0000, 
0x0000, 0x0000, 0x0000, 0x0000, 0xDC90, 0xDC90, 0xFF3B, 0xFF3B, 0xDC90, 0xDC90, 0x0000, 0x0000, 0xFF3B, 0xFF3B, 0x0000, 0x0000, 
0x0000, 0x0000, 0x0000, 0x0000, 0xDC90, 0xDC90, 0xFF3B, 0xFF3B, 0xFF3B, 0xFF3B, 0xDC90, 0xDC90, 0xDC90, 0xDC90, 0xFF3B, 0xFF3B, 
0x0000, 0x0000, 0x0000, 0x0000, 0xDC90, 0xDC90, 0xFF3B, 0xFF3B, 0xFF3B, 0xFF3B, 0xDC90, 0xDC90, 0xDC90, 0xDC90, 0xFF3B, 0xFF3B, 
0x0000, 0x0000, 0x0000, 0x0000, 0x0000, 0x0000, 0xDC90, 0xDC90, 0xFF3B, 0xFF3B, 0xFF3B, 0xFF3B, 0xFF3B, 0xFF3B, 0x0000, 0x0000, 
0x0000, 0x0000, 0x0000, 0x0000, 0x0000, 0x0000, 0xDC90, 0xDC90, 0xFF3B, 0xFF3B, 0xFF3B, 0xFF3B, 0xFF3B, 0xFF3B, 0x0000, 0x0000, 
0x0000, 0x0000, 0xF813, 0xF813, 0xF813, 0xF813, 0xFFEE, 0xFFEE, 0x7EBF, 0x7EBF, 0x7EBF, 0x7EBF, 0xFE60, 0xFE60, 0x0000, 0x0000, 
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
0x0000, 0x0000, 0x0000, 0x0000, 0xF813, 0xF813, 0xF813, 0xF813, 0xF813, 0xF813, 0xF813, 0xF813, 0x0000, 0x0000, 0x0000, 0x0000, 
0x0000, 0x0000, 0x0000, 0x0000, 0xF813, 0xF813, 0xF813, 0xF813, 0xF813, 0xF813, 0xF813, 0xF813, 0x0000, 0x0000, 0x0000, 0x0000
};
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
