vvip-68/GyverMatrixWiFi/firmware/GyverMatrixOS_v1.15/bitmap3.h

const uint16_t ghost00[] PROGMEM = {
0x0000, 0x0000, 0x0000, 0x0000, 0x0000, 0x0000, 0x0000, 0x0000, 0x0000, 0x0000, 0x0000, 0x0000, 0x0000, 0x0000, 0x0000, 0x0000, 
0x0000, 0x0000, 0x0000, 0x0000, 0x0000, 0x0000, 0x0800, 0x0000, 0x0000, 0x0000, 0x0000, 0x0000, 0x0000, 0x0000, 0x0000, 0x0000, 
0x0000, 0x0000, 0x0000, 0x0000, 0x0000, 0x0000, 0x0020, 0xF816, 0xF816, 0xF816, 0xF816, 0x0000, 0x0000, 0x0000, 0x0000, 0x0000, 
0x0000, 0x0000, 0x0000, 0x0000, 0x0002, 0xF816, 0xF816, 0xF816, 0xF816, 0xF816, 0xF816, 0xF816, 0x0000, 0x0000, 0x0000, 0x0000, 
0x0000, 0x0000, 0x0000, 0x0000, 0xF816, 0xF815, 0xF816, 0xF836, 0xF816, 0xF816, 0xF816, 0xF816, 0xF816, 0x0000, 0x0000, 0x0000, 
0x0000, 0x0000, 0x0000, 0xF816, 0xF816, 0xF835, 0xFFFF, 0xFFFF, 0xF816, 0xF816, 0xF816, 0xFFFF, 0xFFFF, 0xF816, 0x0000, 0x0000, 
0x0000, 0x0000, 0x0000, 0xF816, 0xF816, 0xFFFF, 0xFFFF, 0xFFFF, 0xFFFF, 0xF816, 0xFFFF, 0xFFFF, 0xFFFF, 0xFFFF, 0x0000, 0x0000, 
0x0000, 0x0000, 0x0000, 0xF816, 0xF816, 0xFFFF, 0xFFFF, 0x04BD, 0x04BD, 0xF816, 0xFFFF, 0xFFFF, 0x04BD, 0x04BD, 0x0000, 0x0000, 
0x0000, 0x0000, 0xF816, 0xF816, 0xF836, 0xFFFF, 0xFFFF, 0x04BD, 0x0CBD, 0xF816, 0xFFFF, 0xFFFF, 0x04BD, 0x04BD, 0xF816, 0x0000, 
0x0000, 0x0000, 0xF816, 0xF816, 0xF816, 0xF816, 0xFFFF, 0xFFFF, 0xF816, 0xF816, 0xF816, 0xFFFF, 0xFFFF, 0xF816, 0xF816, 0x0000, 
0x0000, 0x0000, 0xF816, 0xF816, 0xF816, 0xF816, 0xF816, 0xF816, 0xF816, 0xF816, 0xF816, 0xF816, 0xF816, 0xF816, 0xF816, 0x0000, 
0x0000, 0x0000, 0xF816, 0xF816, 0xF816, 0xF816, 0xF816, 0xF816, 0xF816, 0xF816, 0xF816, 0xF816, 0xF816, 0xF816, 0xF816, 0x0000, 
0x0000, 0x0000, 0xF816, 0xF816, 0xF816, 0xF816, 0xF816, 0xF816, 0xF816, 0xF816, 0xF816, 0xF816, 0xF816, 0xF816, 0xF816, 0x0000, 
0x0000, 0x0000, 0xF816, 0xF816, 0x0000, 0xF816, 0xF816, 0xF816, 0x0000, 0x0000, 0xF816, 0xF816, 0x0000, 0xF816, 0xF816, 0x0000, 
0x0000, 0x0000, 0xF816, 0x0000, 0x0000, 0x0000, 0xF816, 0xF816, 0x0000, 0x0000, 0xF816, 0x0000, 0x0000, 0x0000, 0xF816, 0x0000, 
0x0000, 0x0000, 0x0000, 0x0000, 0x0000, 0x0000, 0x0000, 0x0000, 0x0000, 0x0000, 0x0000, 0x0000, 0x0000, 0x0000, 0x0000, 0x0000
};

const uint16_t* const ghost_array[1] PROGMEM =   {
ghost00};
